AmigusLabs/Boya-Lora/images/IMG_3274.jpg

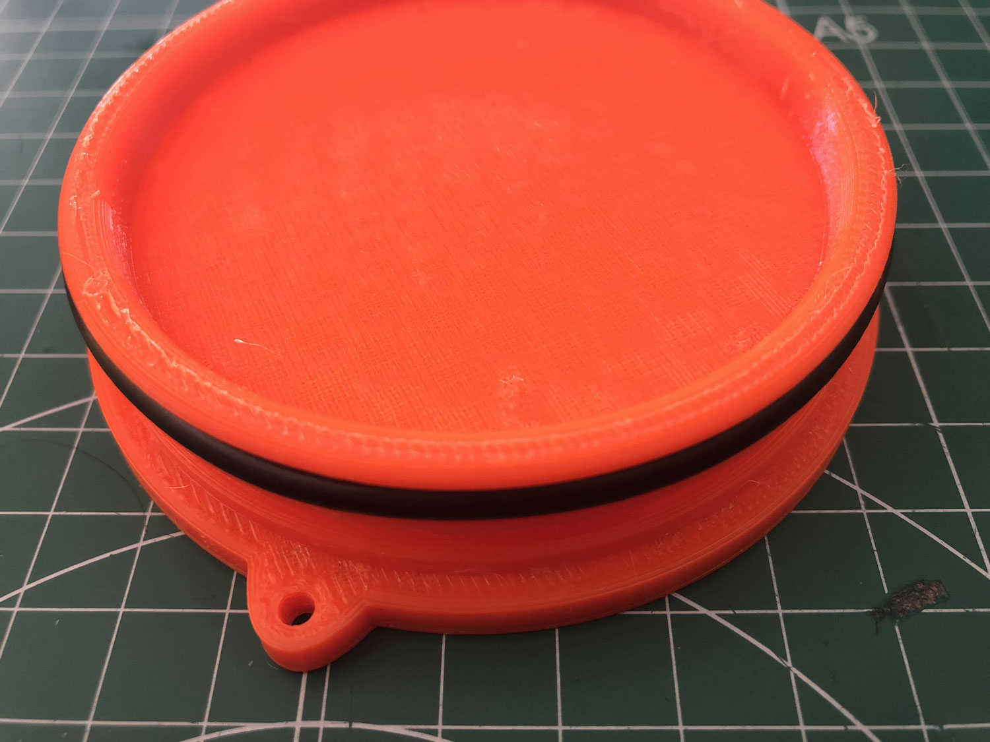
images/IMG_3274.jpg
