AmigusLabs/Boya-Lora/images/IMG_3366.jpg

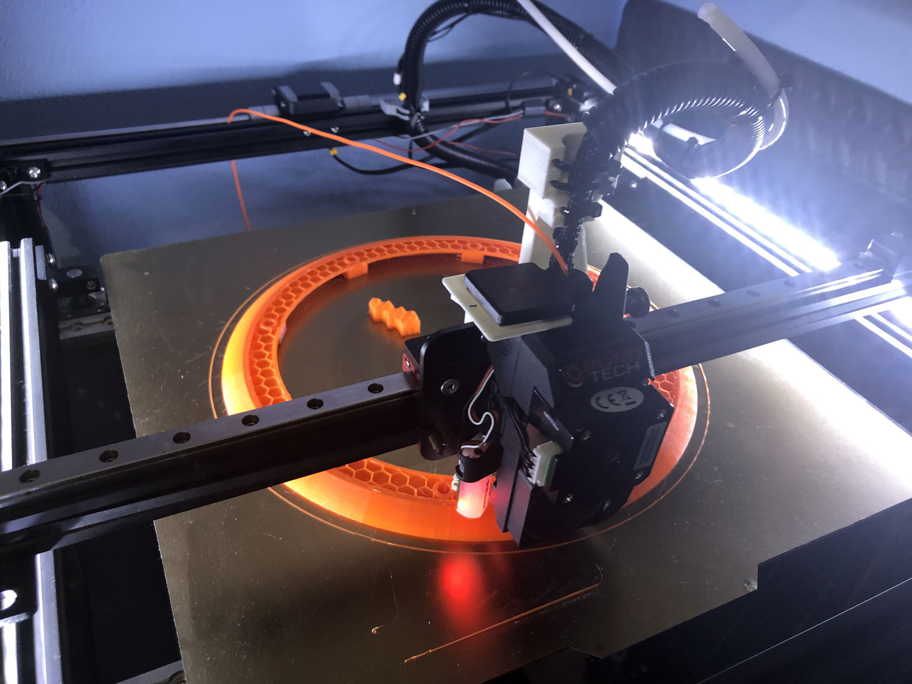
images/IMG_3366.jpg
