AmigusLabs/Boya-Lora/images/IMG_3369.jpg

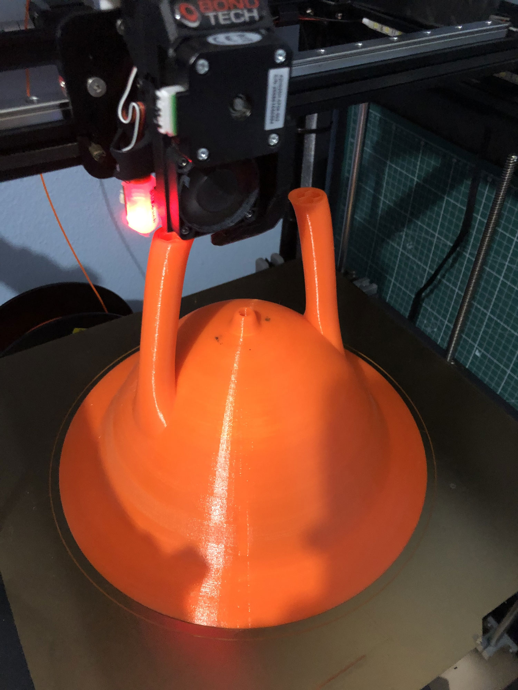
images/IMG_3369.jpg
