AmigusLabs/Boya-Lora/images/IMG_3554.jpg

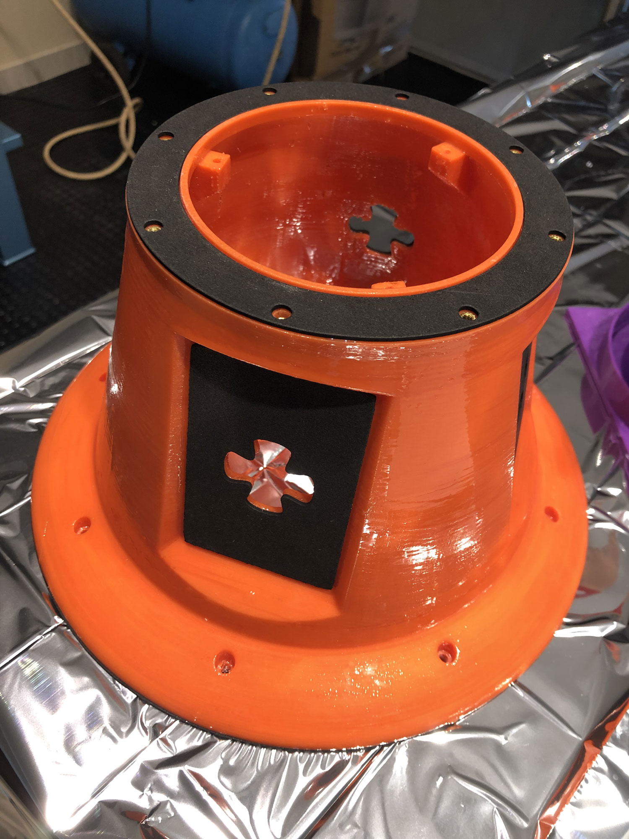
images/IMG_3554.jpg
