AmigusLabs/Boya-Lora/images/IMG_3555.jpg

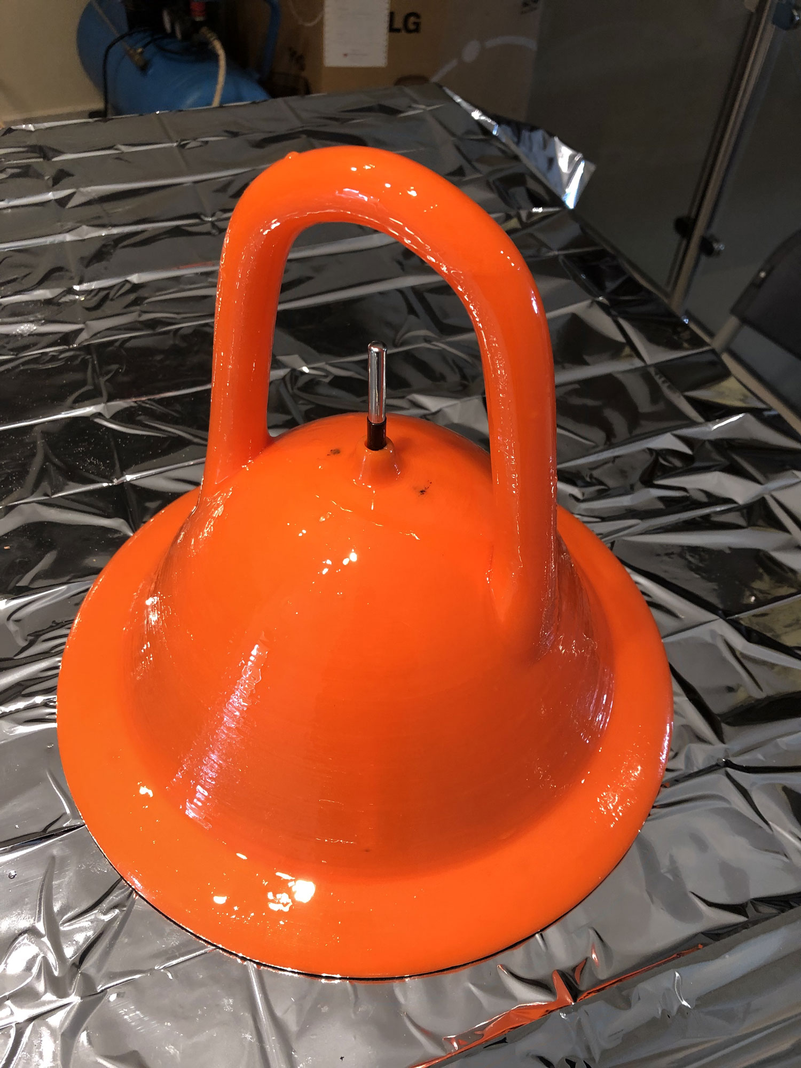
images/IMG_3555.jpg
