AmigusLabs/Boya-Lora/images/IMG_3556.jpg

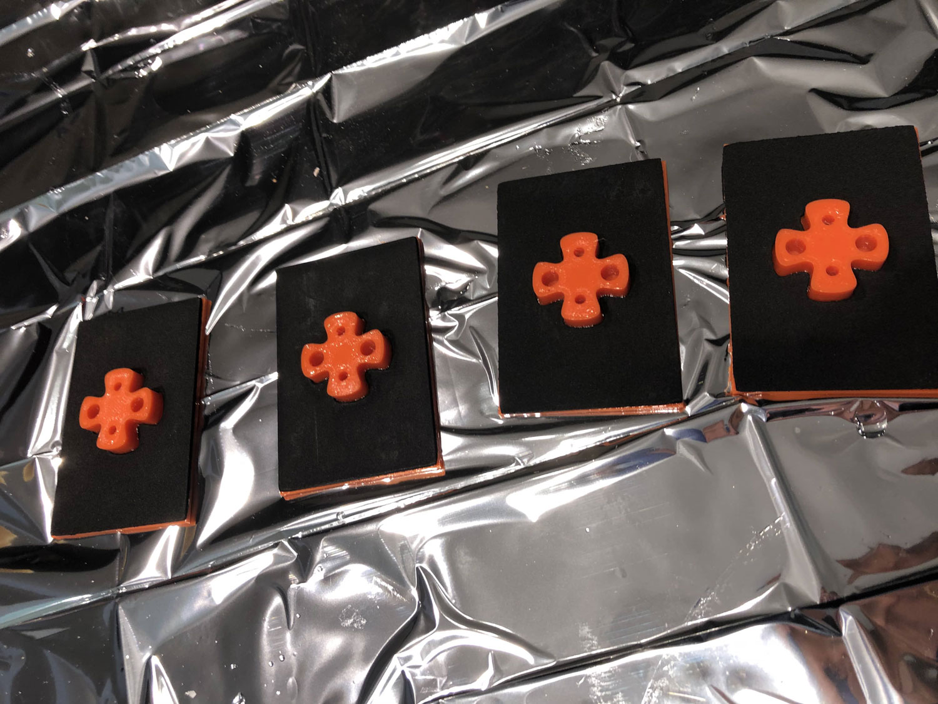
images/IMG_3556.jpg
