AmigusLabs/Boya-Lora/images/IMG_3557.jpg

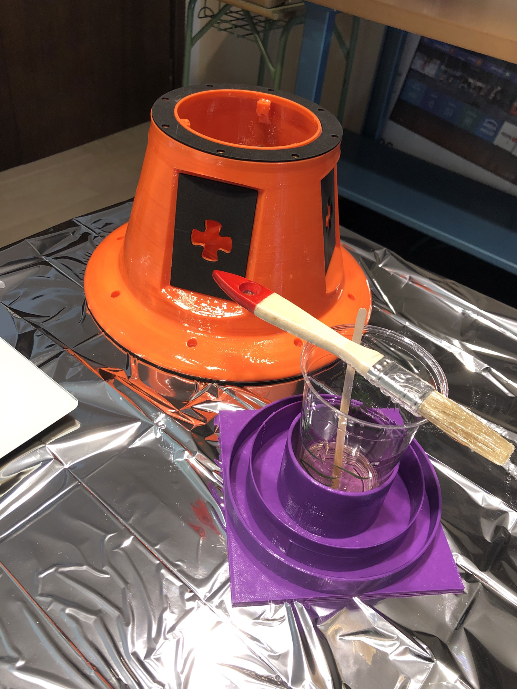
images/IMG_3557.jpg
