AmigusLabs/Boya-Lora/images/IMG_3694.jpg

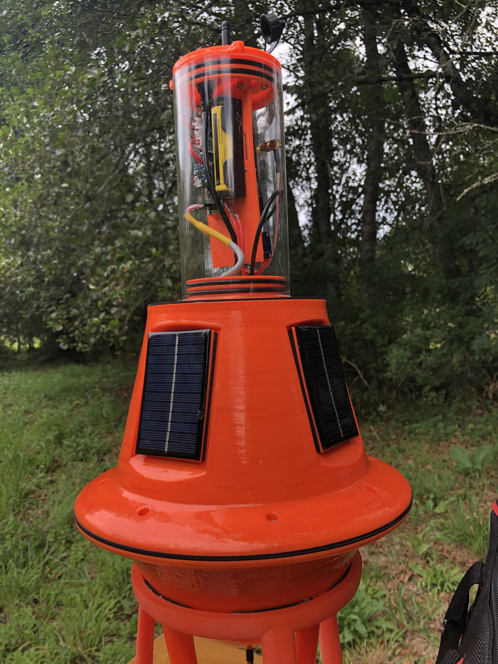
images/IMG_3694.jpg
